mircose/ESP32_MP/TestSketch/TestAnalogButton/AnalogButtonSerialMonitor.png

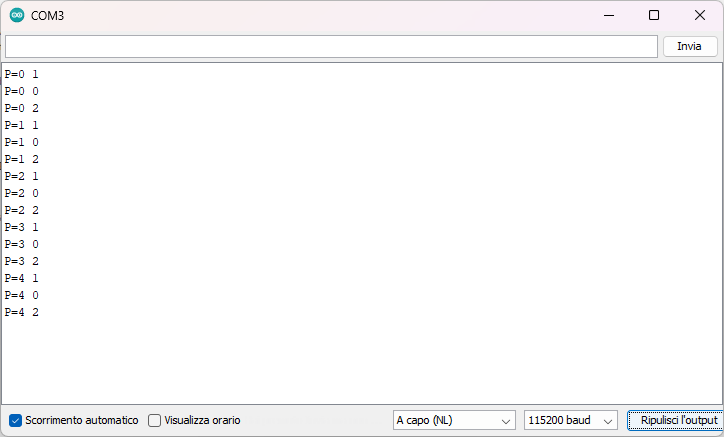
TestSketch/TestAnalogButton/AnalogButtonSerialMonitor.png
