mircose/ESP32_MP/TestSketch/TestSD_EXT/TESTSD_EXT_SerialMonitor.png

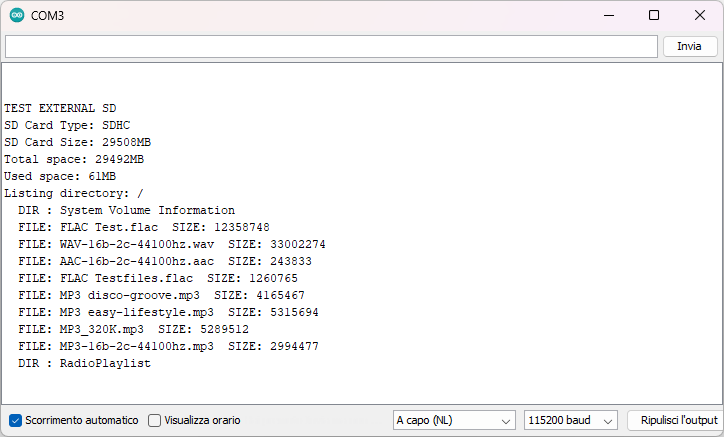
TestSketch/TestSD_EXT/TESTSD_EXT_SerialMonitor.png
